NikolaiRadke/Noko/Schematics/kicad/screenshots/NOKO PCB Layout 2018-02-01 20-47-03.png

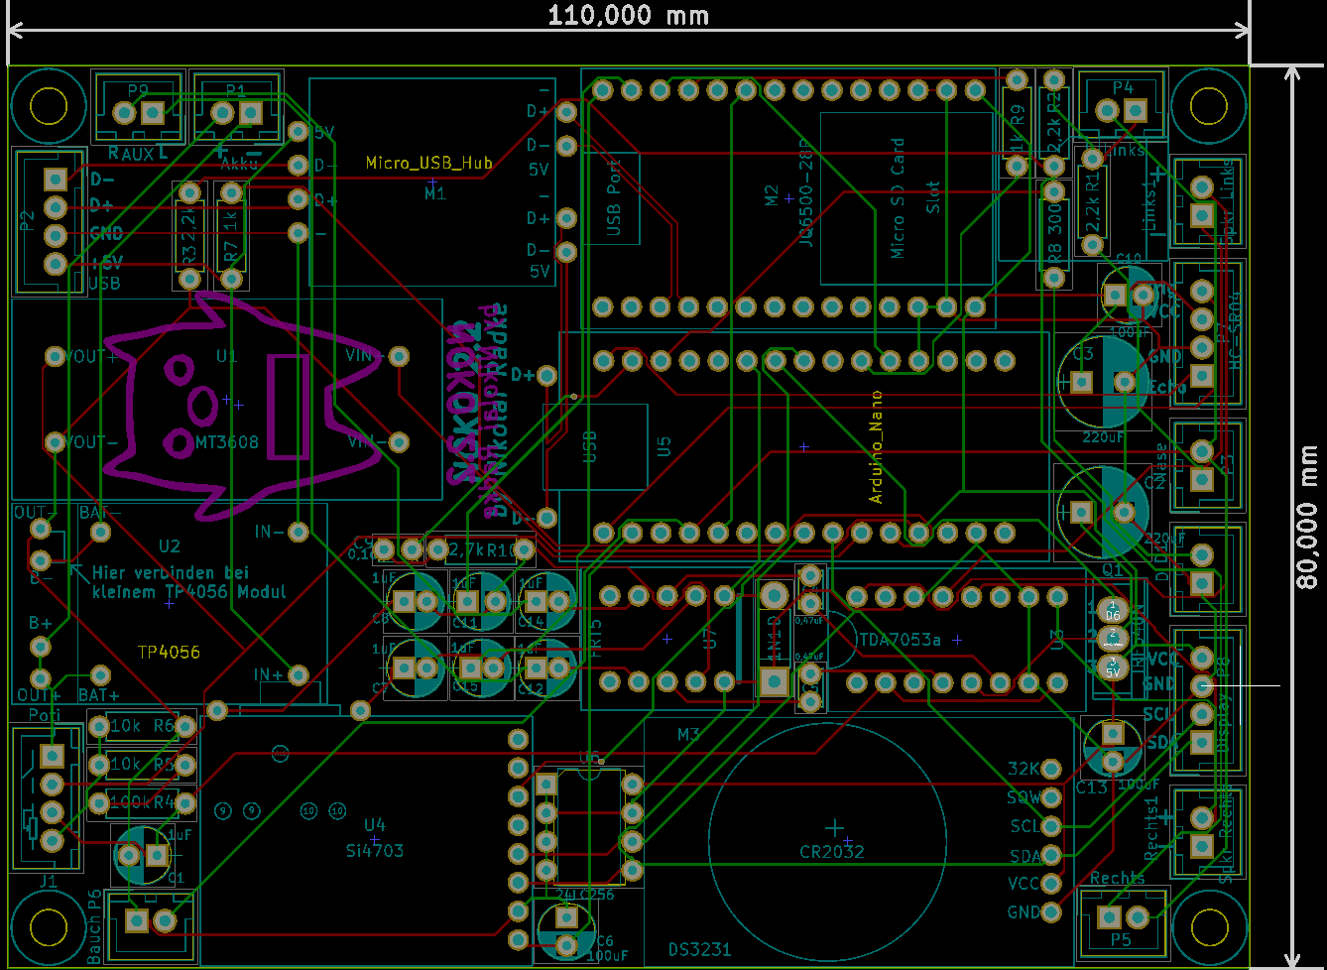
Schematics/kicad/screenshots/NOKO PCB Layout 2018-02-01 20-47-03.png
