NikolaiRadke/Noko/schematics/Noko.png

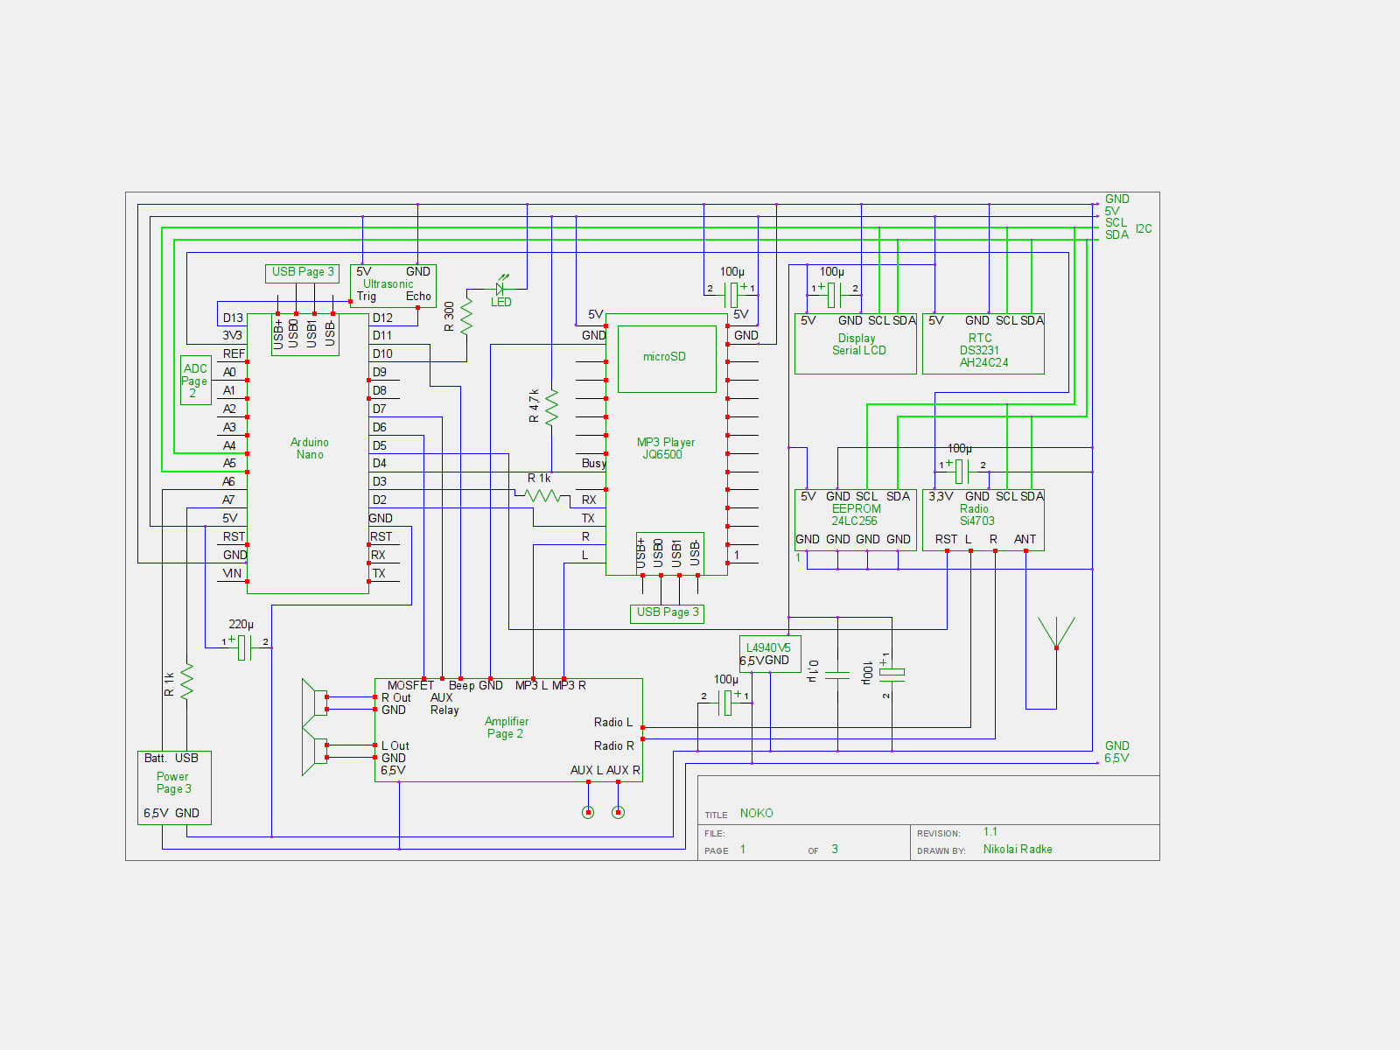
schematics/Noko.png
