NikolaiRadke/Noko/schematics/Noko_layout_poti.png

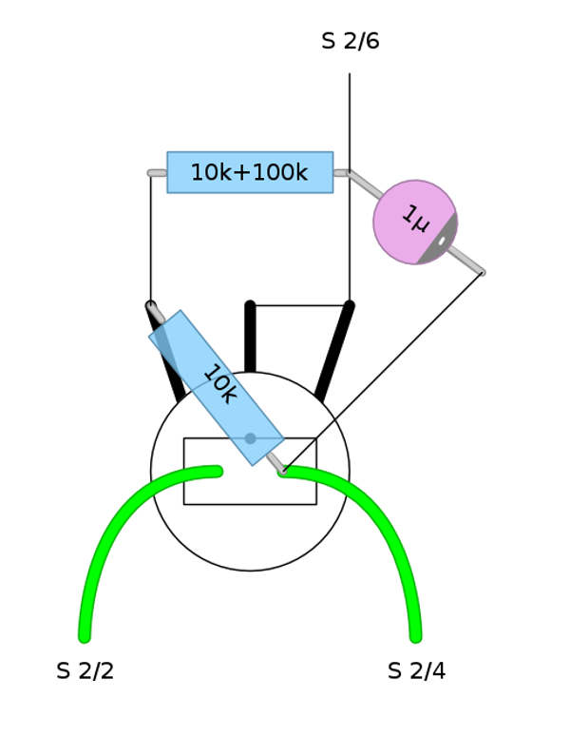
schematics/Noko_layout_poti.png
