NikolaiRadke/Noko/Schematics/NOKO_layout_s1.png

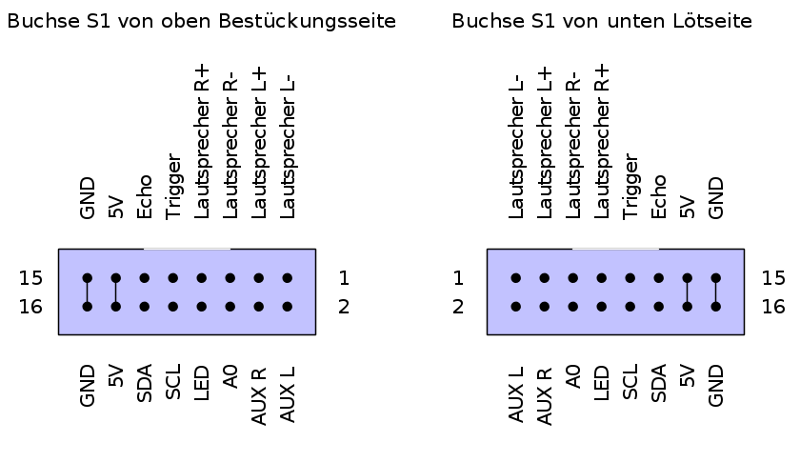
Schematics/NOKO_layout_s1.png
