NikolaiRadke/Noko/schematics/Noko_layout_s2.png

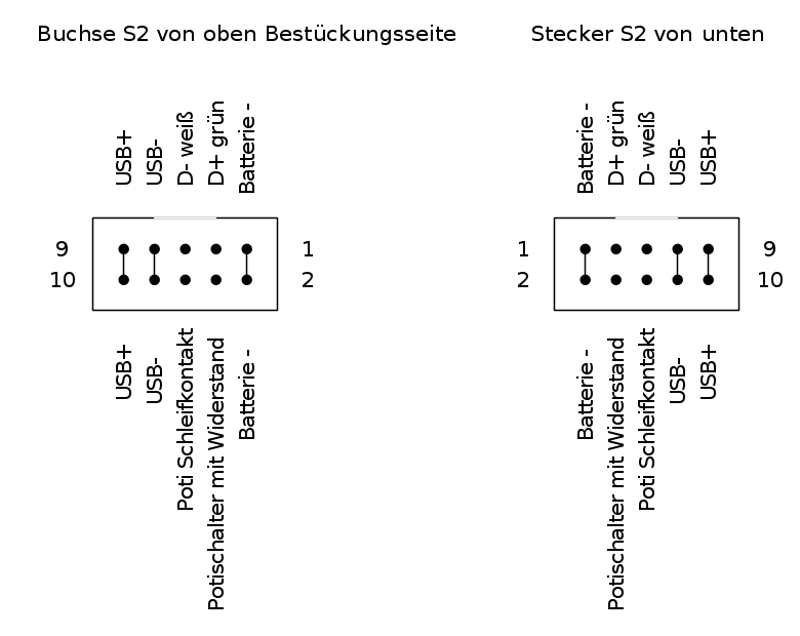
schematics/Noko_layout_s2.png
