NikolaiRadke/Noko/schematics/Noko_layout_small_2.png

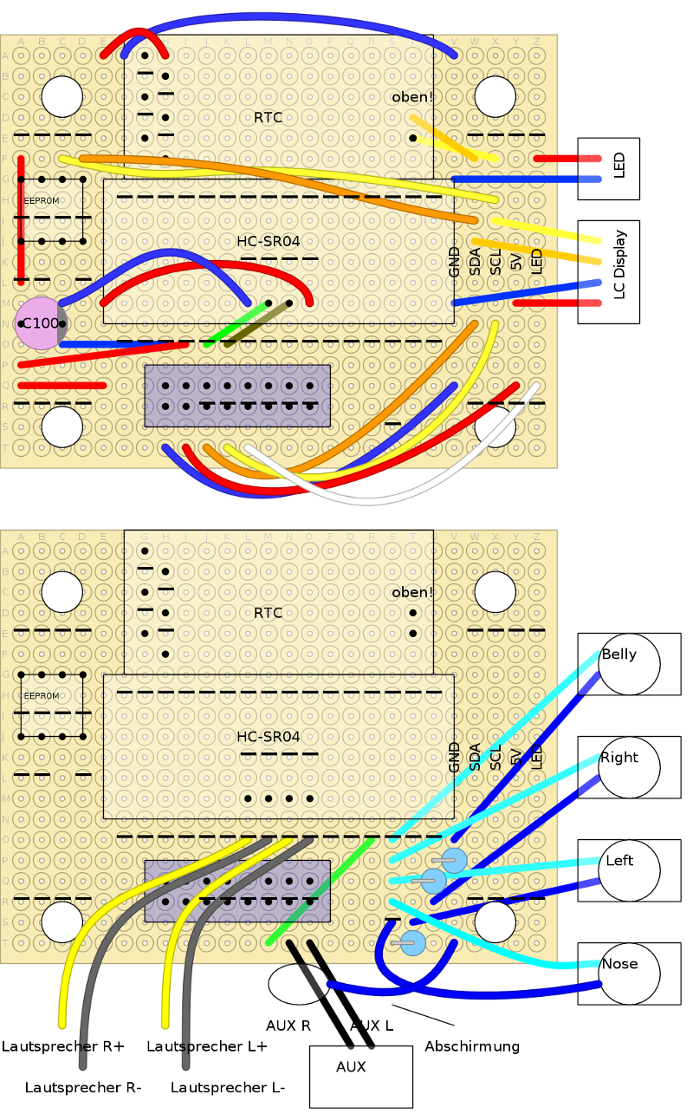
schematics/Noko_layout_small_2.png
