NikolaiRadke/Noko/schematics/Noko_layout_up.png

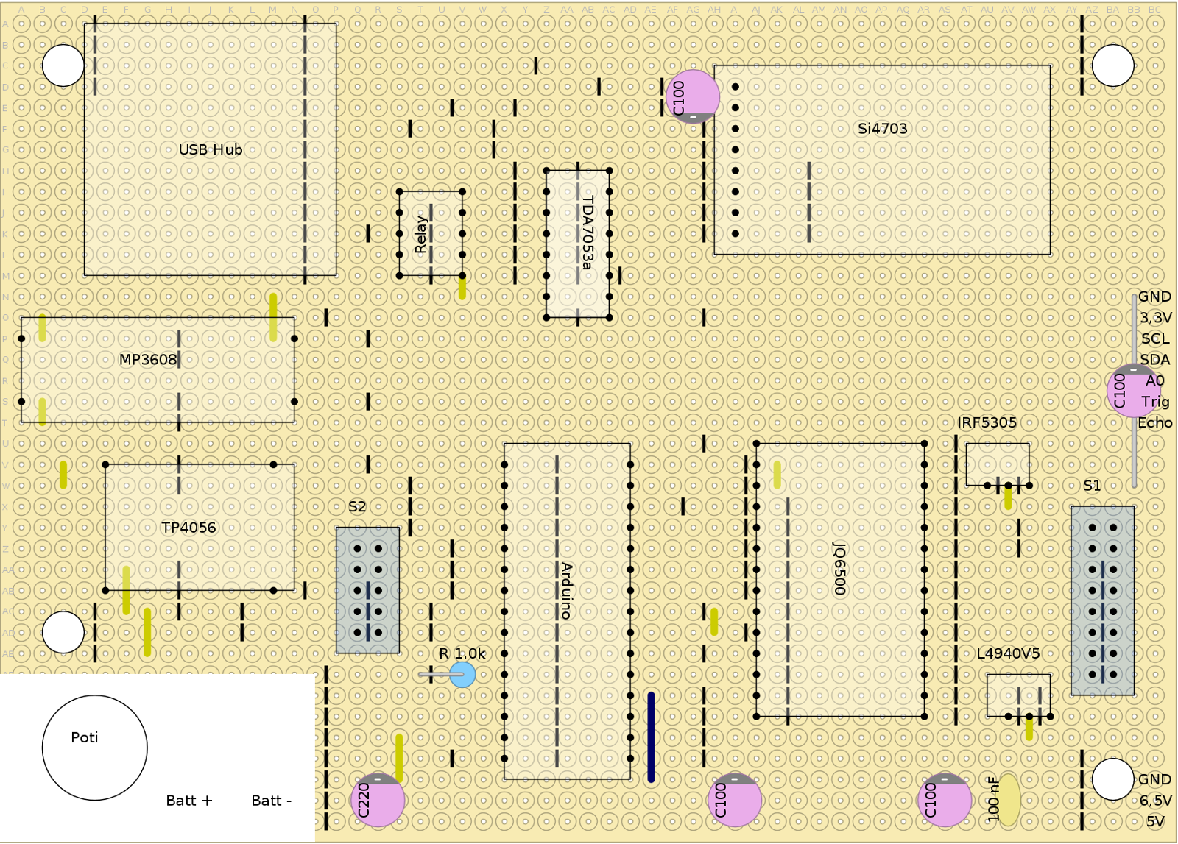
schematics/Noko_layout_up.png
