NikolaiRadke/Noko/schematics/Noko_layout_up_data.png

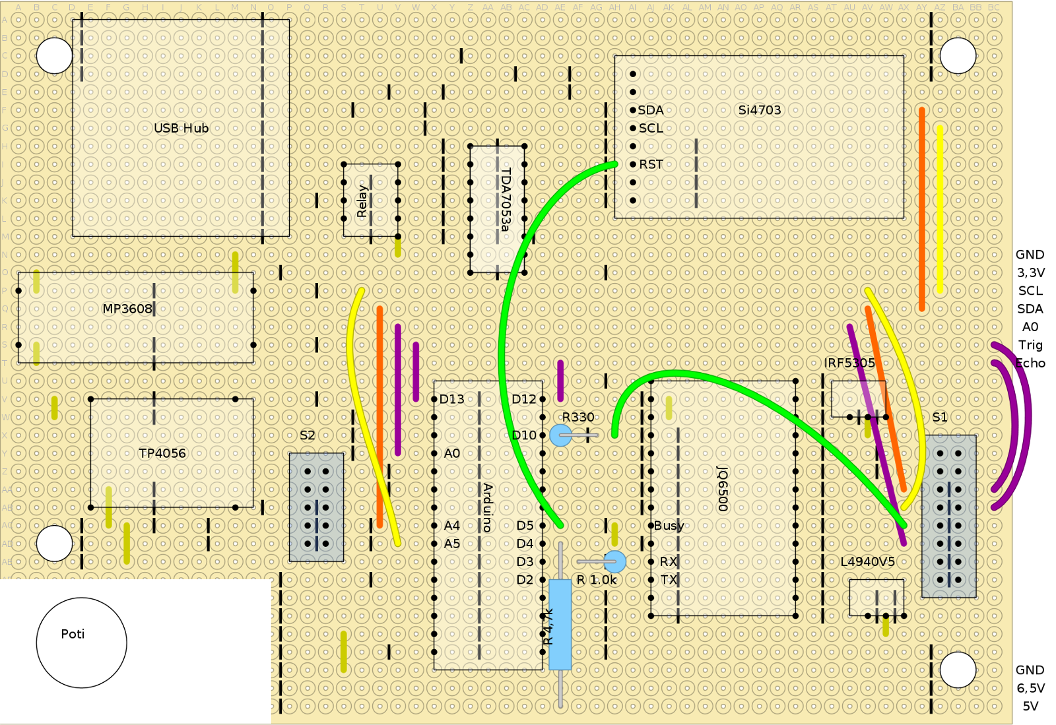
schematics/Noko_layout_up_data.png
