NikolaiRadke/Noko/schematics/Noko_layout_up_power.png

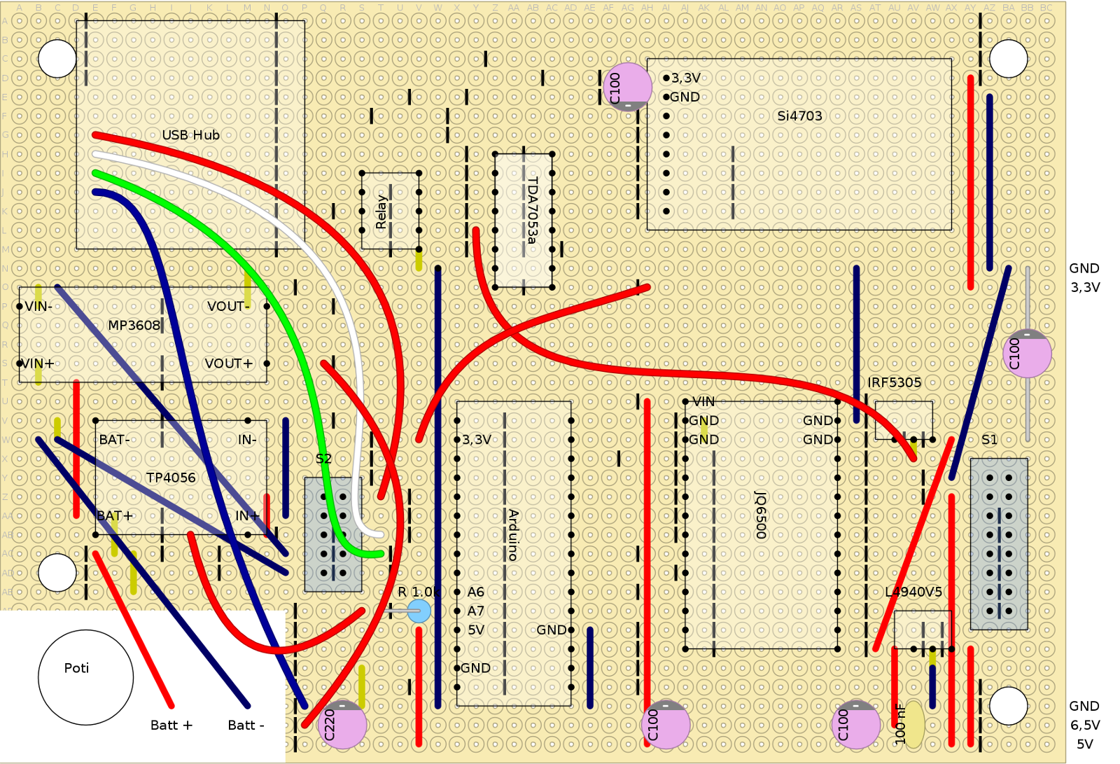
schematics/Noko_layout_up_power.png
