NikolaiRadke/Noko/schematics/Noko_raw.png

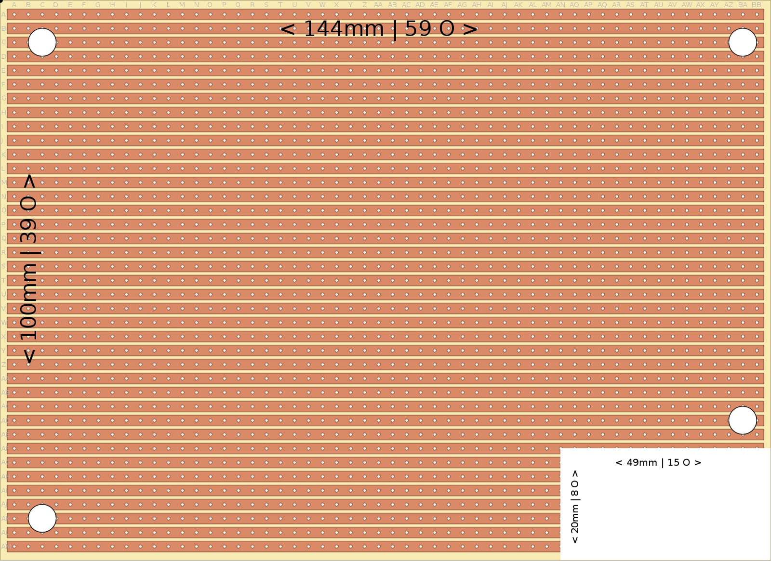
schematics/Noko_raw.png
