NikolaiRadke/Noko/schematics/Noko_USB.png

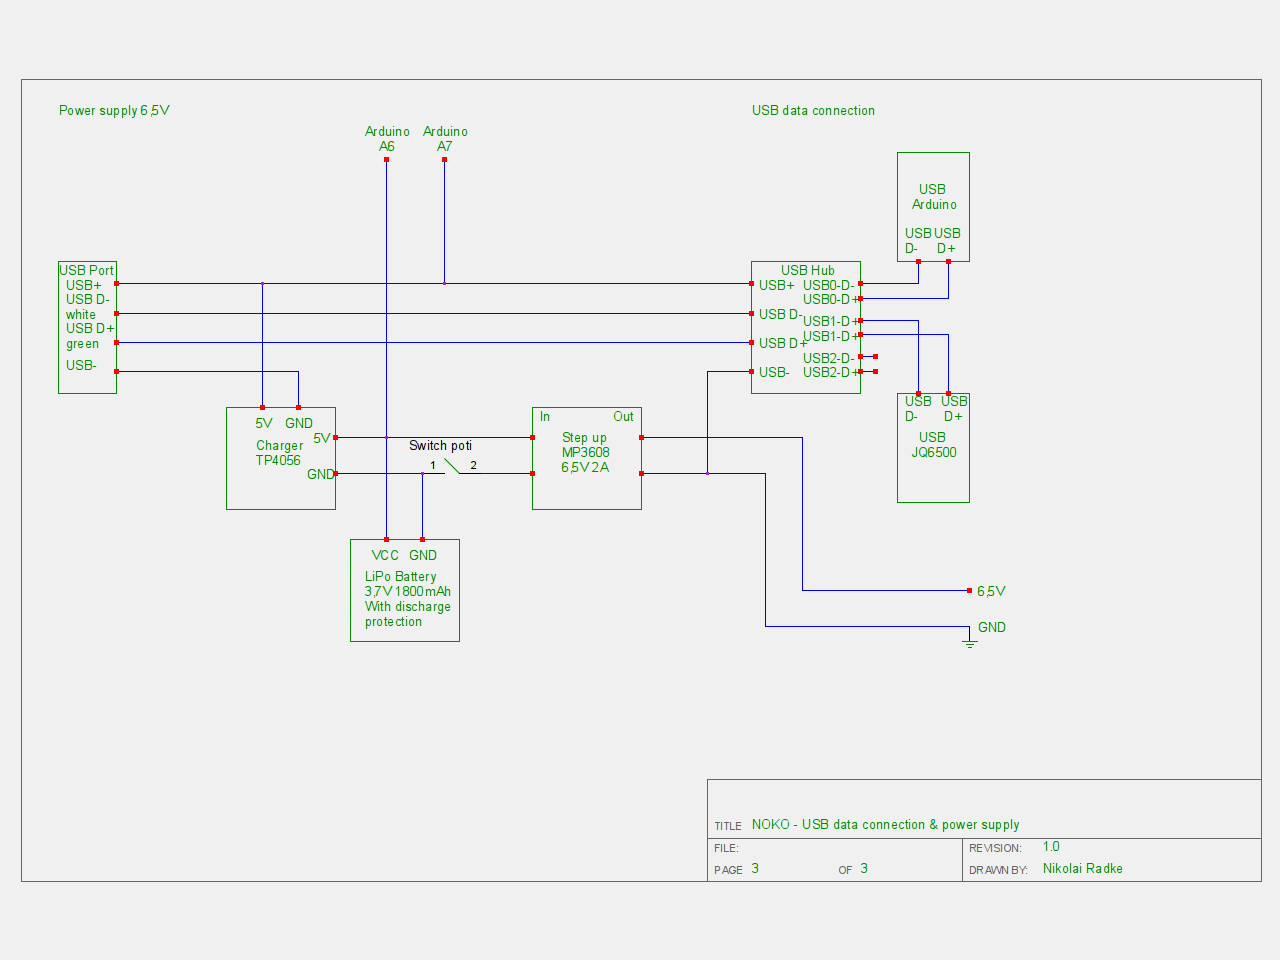
schematics/Noko_USB.png
