NikolaiRadke/Noko/Manual/scribus/noko_bauchtaste.png

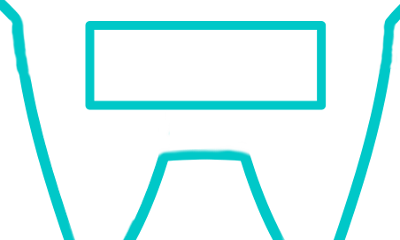
Manual/scribus/noko_bauchtaste.png
