NikolaiRadke/Noko/Manual/scribus/noko_buchse.png

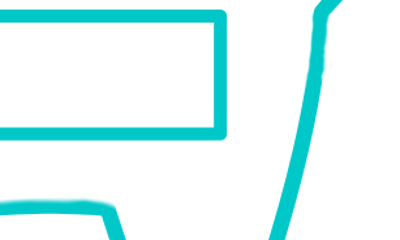
Manual/scribus/noko_buchse.png
