NikolaiRadke/Noko/Manual/scribus/noko_display.png

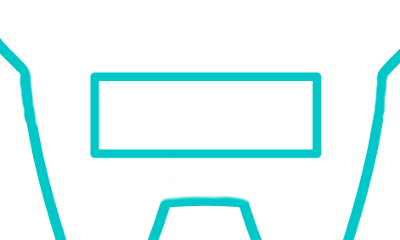
Manual/scribus/noko_display.png
