NikolaiRadke/Noko/Manual/scribus/noko_distanz.png

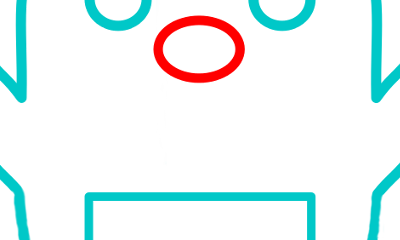
Manual/scribus/noko_distanz.png
