NikolaiRadke/Noko/Manual/scribus/noko_dreitasten.png

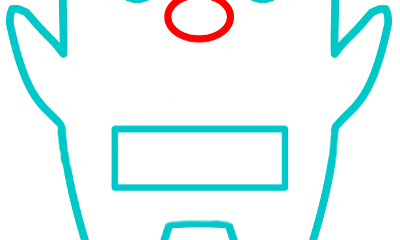
Manual/scribus/noko_dreitasten.png
