NikolaiRadke/Noko/Manual/scribus/noko_lautsprecher.png

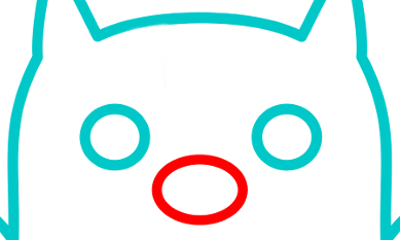
Manual/scribus/noko_lautsprecher.png
