NikolaiRadke/Noko/Manual/scribus/noko_links.png

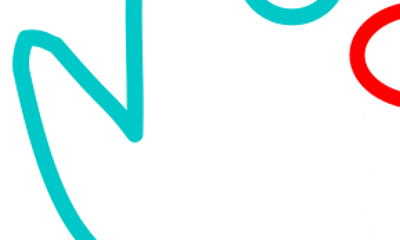
Manual/scribus/noko_links.png
