NikolaiRadke/Noko/Manual/scribus/noko_nase.png

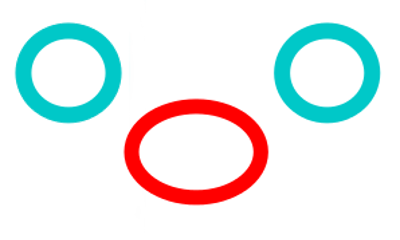
Manual/scribus/noko_nase.png
