NikolaiRadke/Noko/Manual/scribus/noko_rechts.png

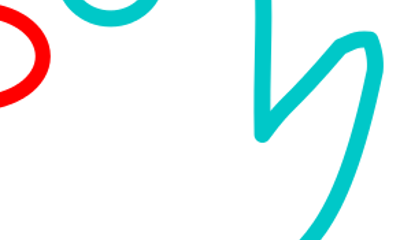
Manual/scribus/noko_rechts.png
