NikolaiRadke/Noko/Manual/scribus/noko_uhrzeit.png

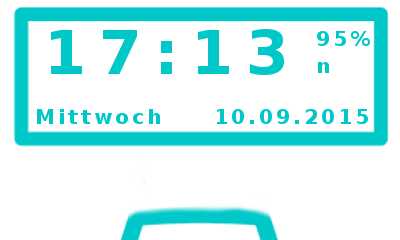
Manual/scribus/noko_uhrzeit.png
